n01060890/n01060890.github.io/code/html/hive.jpg

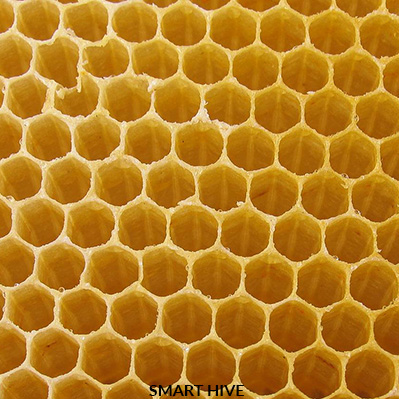
code/html/hive.jpg
