n01060890/n01060890.github.io/media/budget.jpg

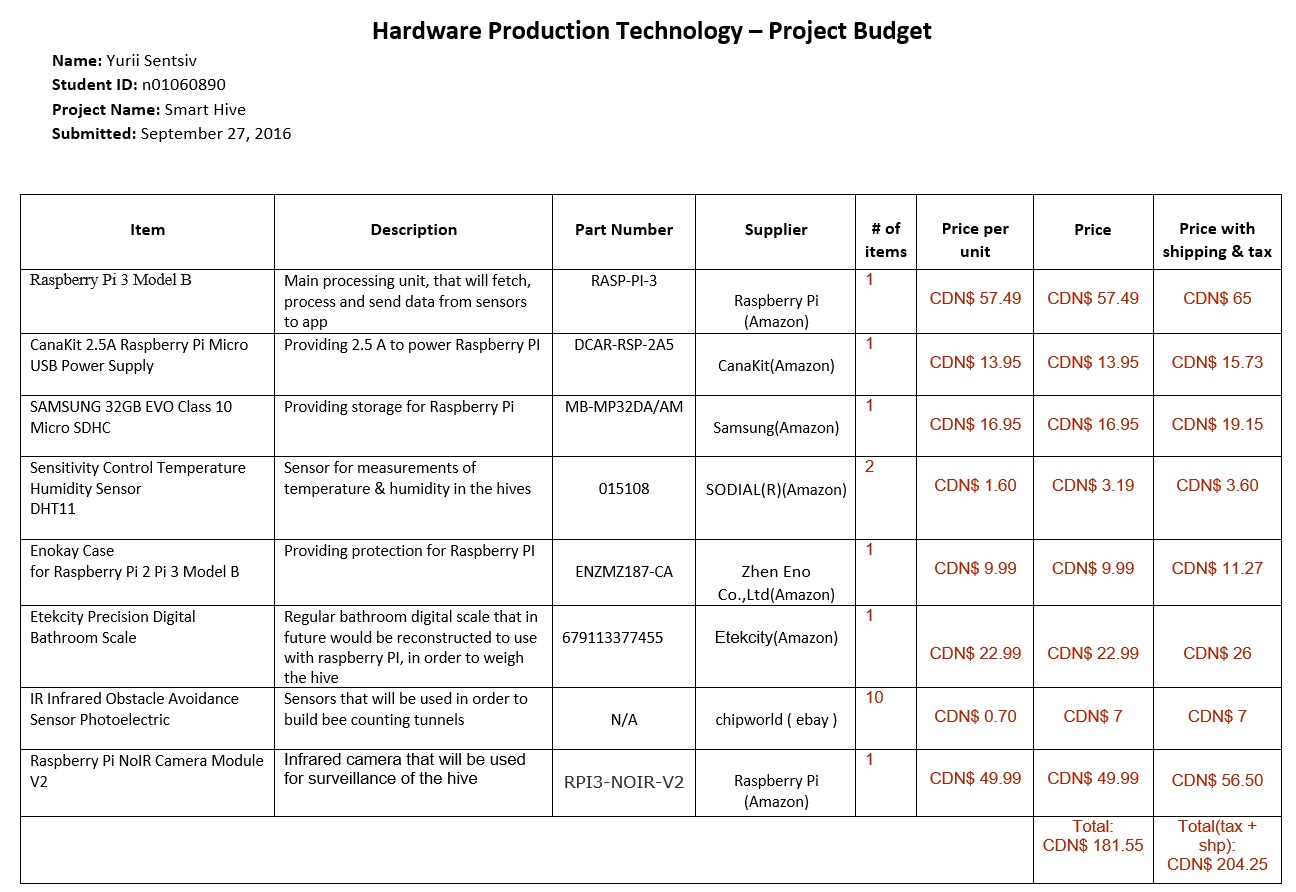
media/budget.jpg
