n01060890/n01060890.github.io/media/case.jpg

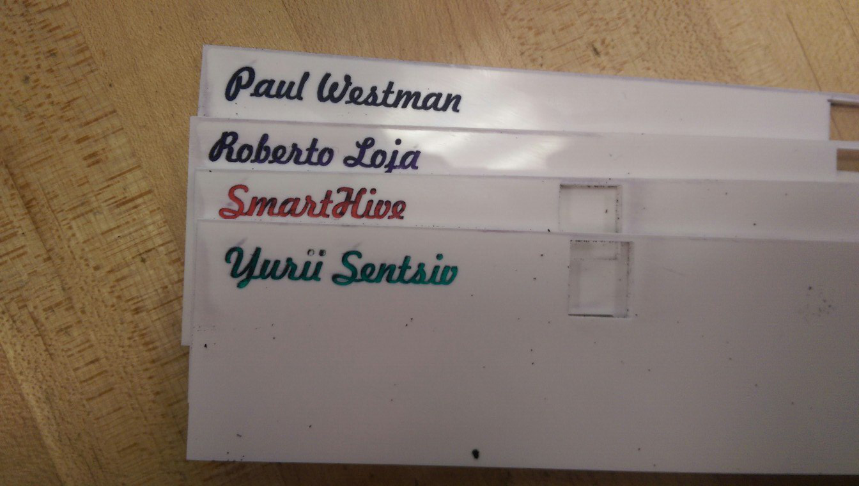
media/case.jpg
