n01060890/n01060890.github.io/media/cluster.png

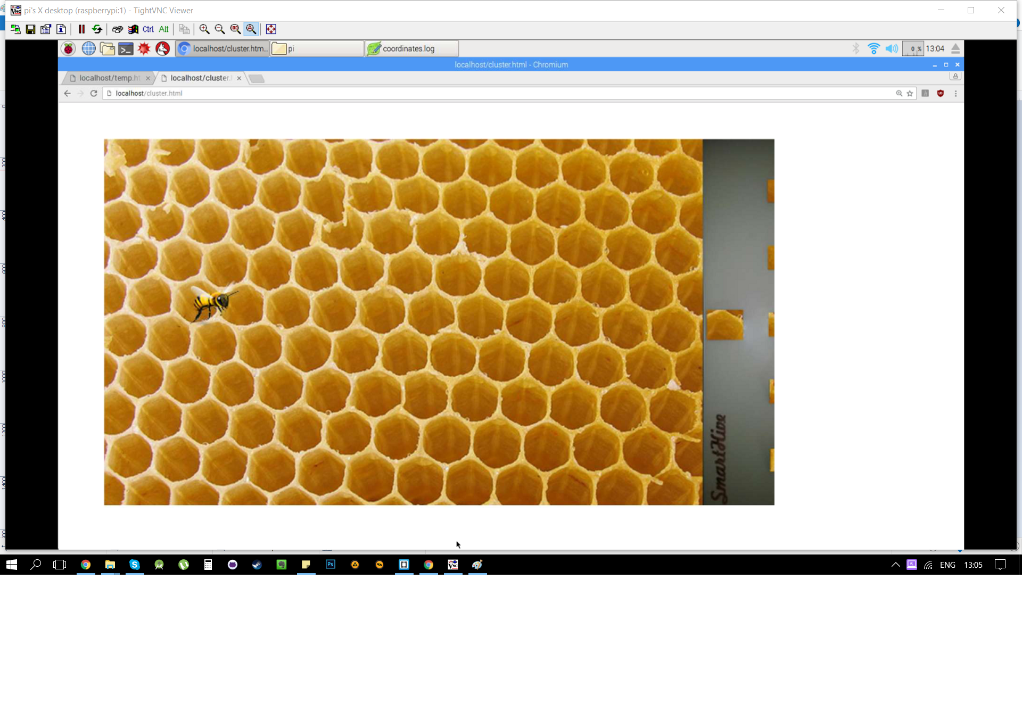
media/cluster.png
