n01060890/n01060890.github.io/media/crontab.png

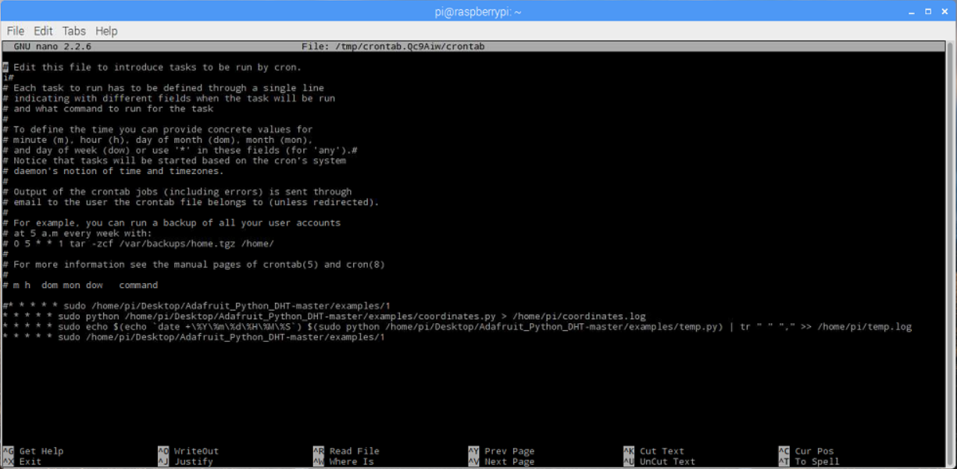
media/crontab.png
