n01060890/n01060890.github.io/media/DHT11.jpg

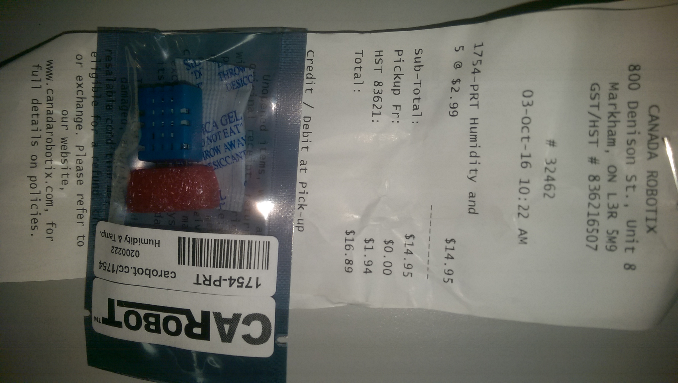
media/DHT11.jpg
