n01060890/n01060890.github.io/media/dht11_pcb.jpg

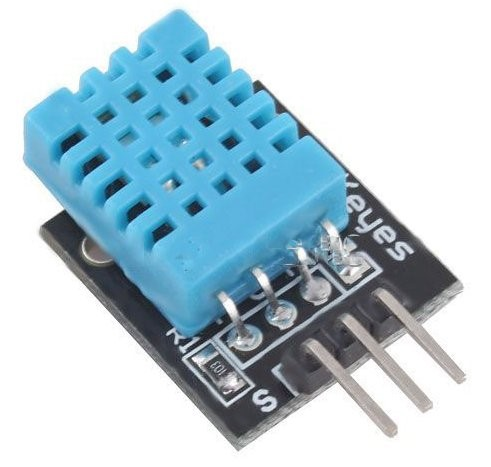
media/dht11_pcb.jpg
