n01060890/n01060890.github.io/media/dht11_pcb_mine.png

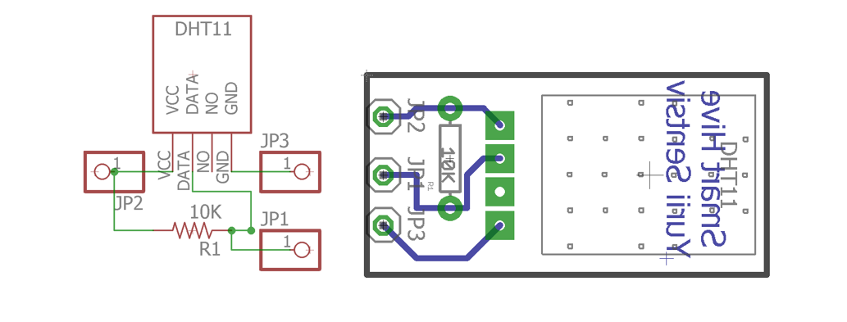
media/dht11_pcb_mine.png
