n01060890/n01060890.github.io/media/dht11_taped.jpg

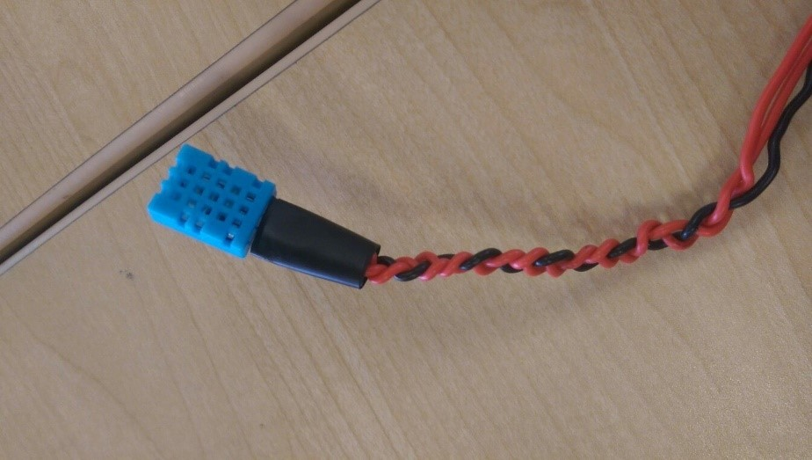
media/dht11_taped.jpg
