n01060890/n01060890.github.io/media/laser_cut.png

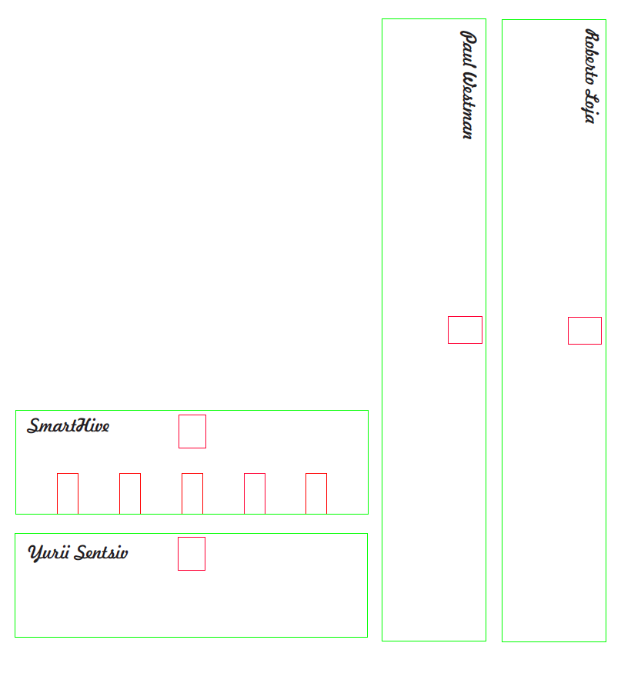
media/laser_cut.png
