n01060890/n01060890.github.io/media/LEDBLINK.jpg

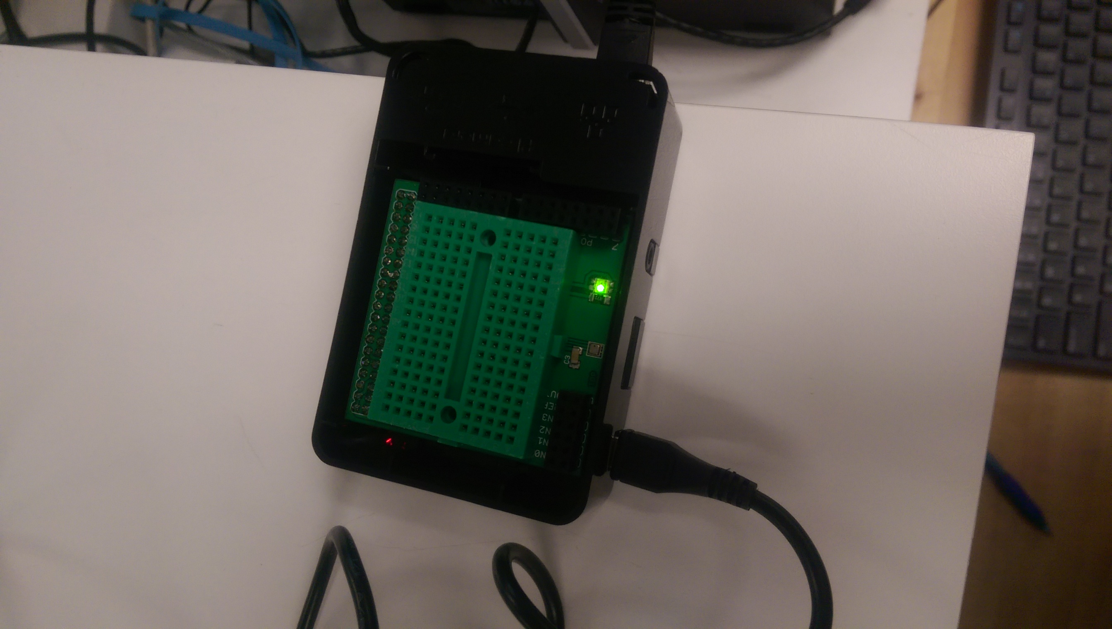
media/LEDBLINK.jpg
