n01060890/n01060890.github.io/media/MultiSensor1.jpg

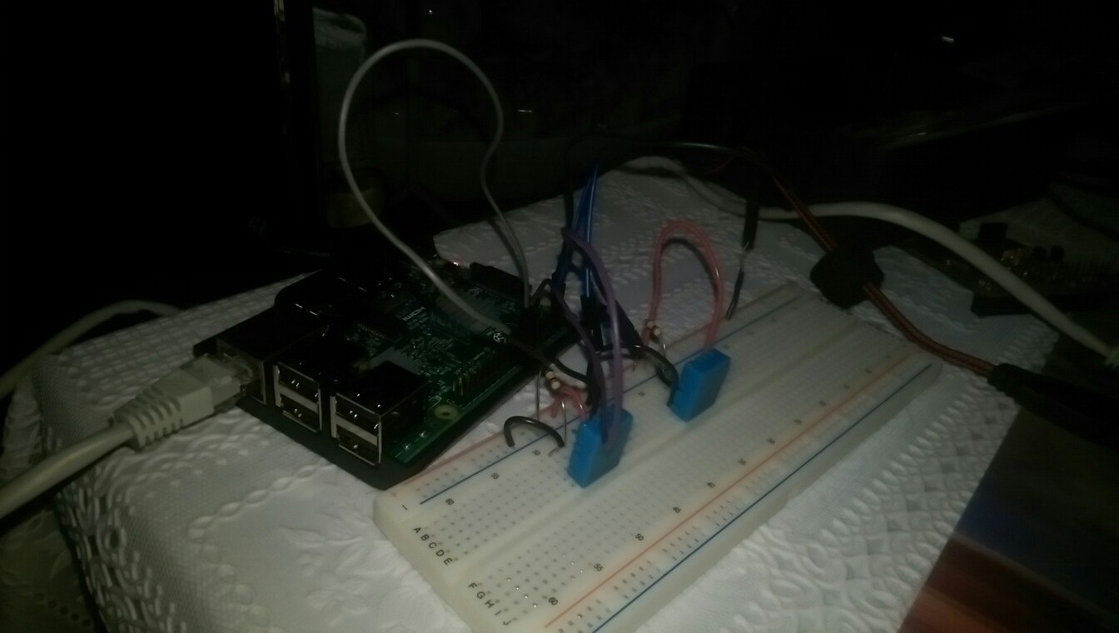
media/MultiSensor1.jpg
