n01060890/n01060890.github.io/media/MultiSensor2.jpg

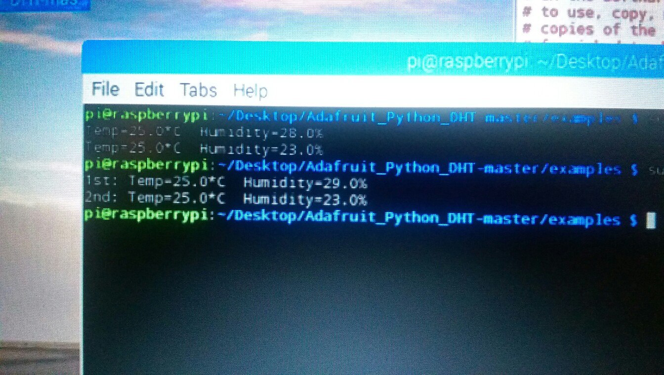
media/MultiSensor2.jpg
