n01060890/n01060890.github.io/media/myPCB.jpg

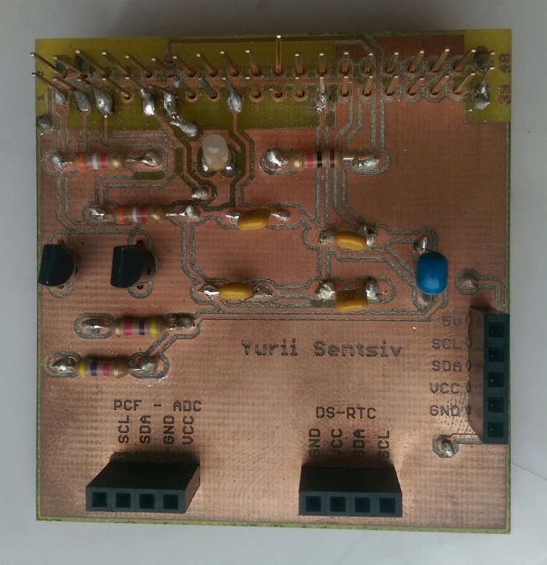
media/myPCB.jpg
