n01060890/n01060890.github.io/media/OHouse1.jpg

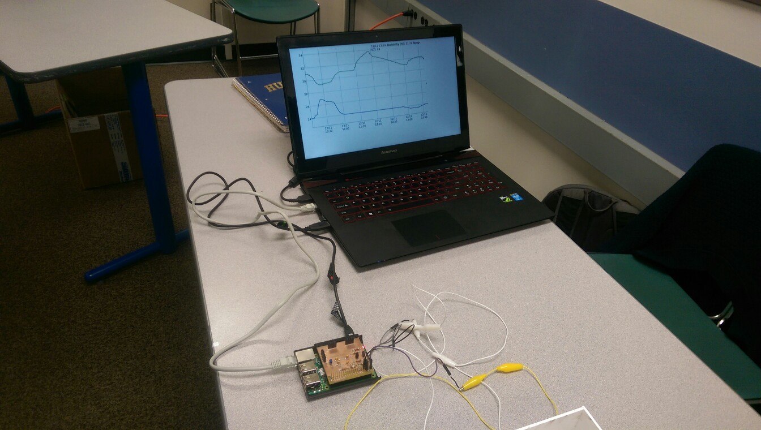
media/OHouse1.jpg
