n01060890/n01060890.github.io/media/OHouse2.jpg

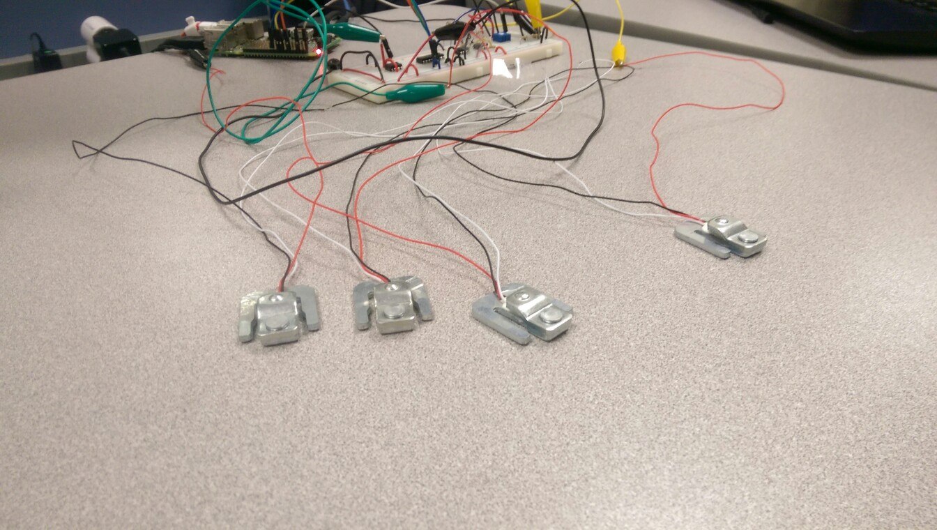
media/OHouse2.jpg
