n01060890/n01060890.github.io/media/OHouse3.jpg

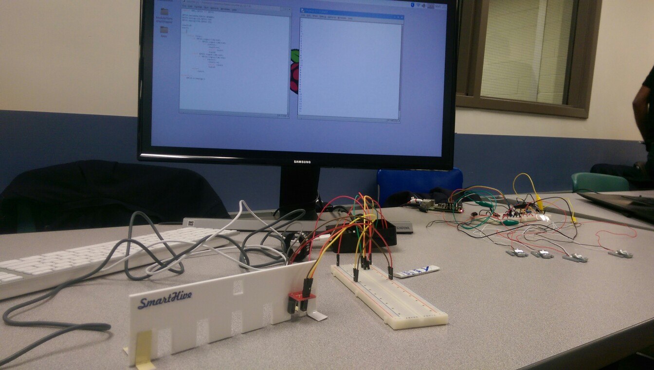
media/OHouse3.jpg
