n01060890/n01060890.github.io/media/output_screen.png

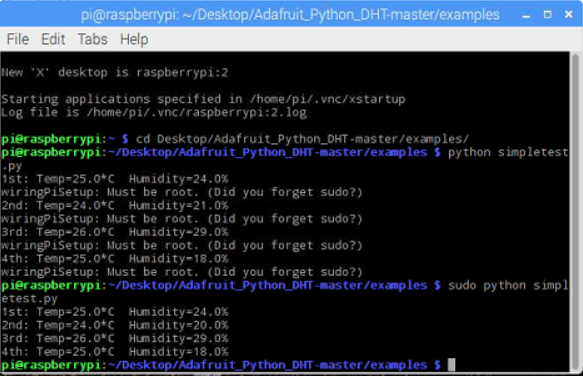
media/output_screen.png
