n01060890/n01060890.github.io/media/PCB_board.png

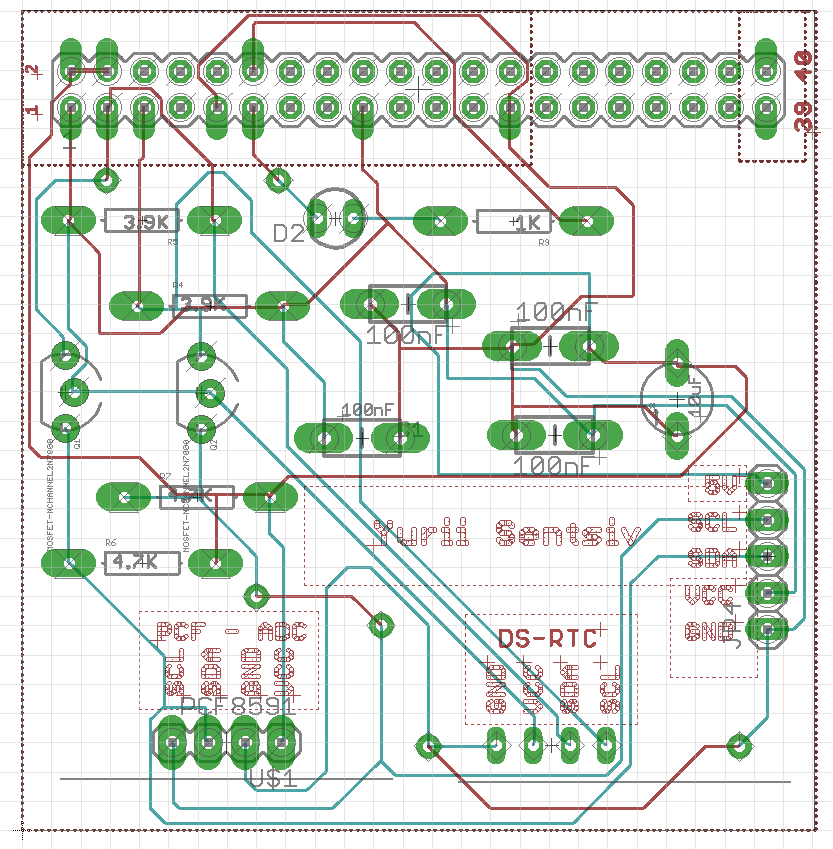
media/PCB_board.png
