n01060890/n01060890.github.io/media/PCB_scheme.png

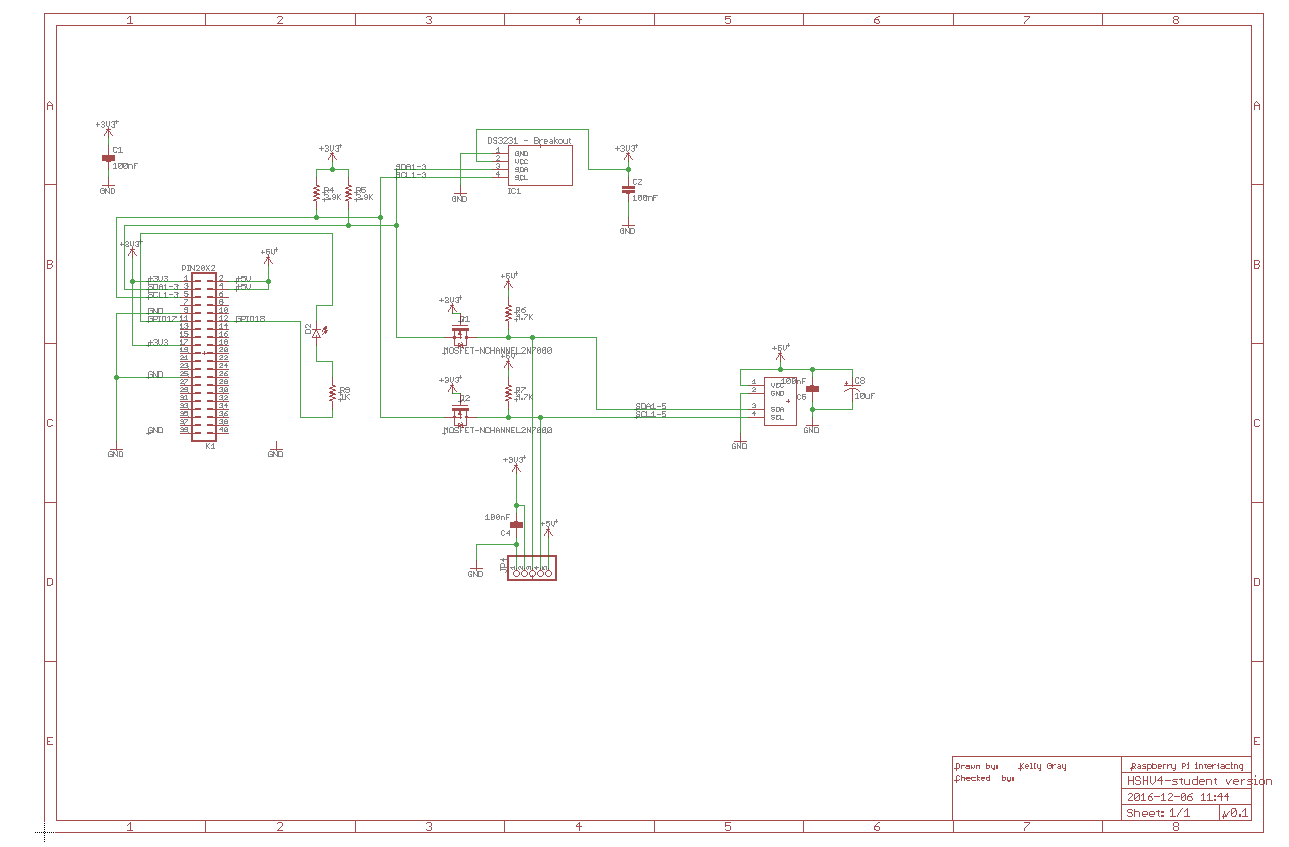
media/PCB_scheme.png
