n01060890/n01060890.github.io/media/project-scedule.jpg

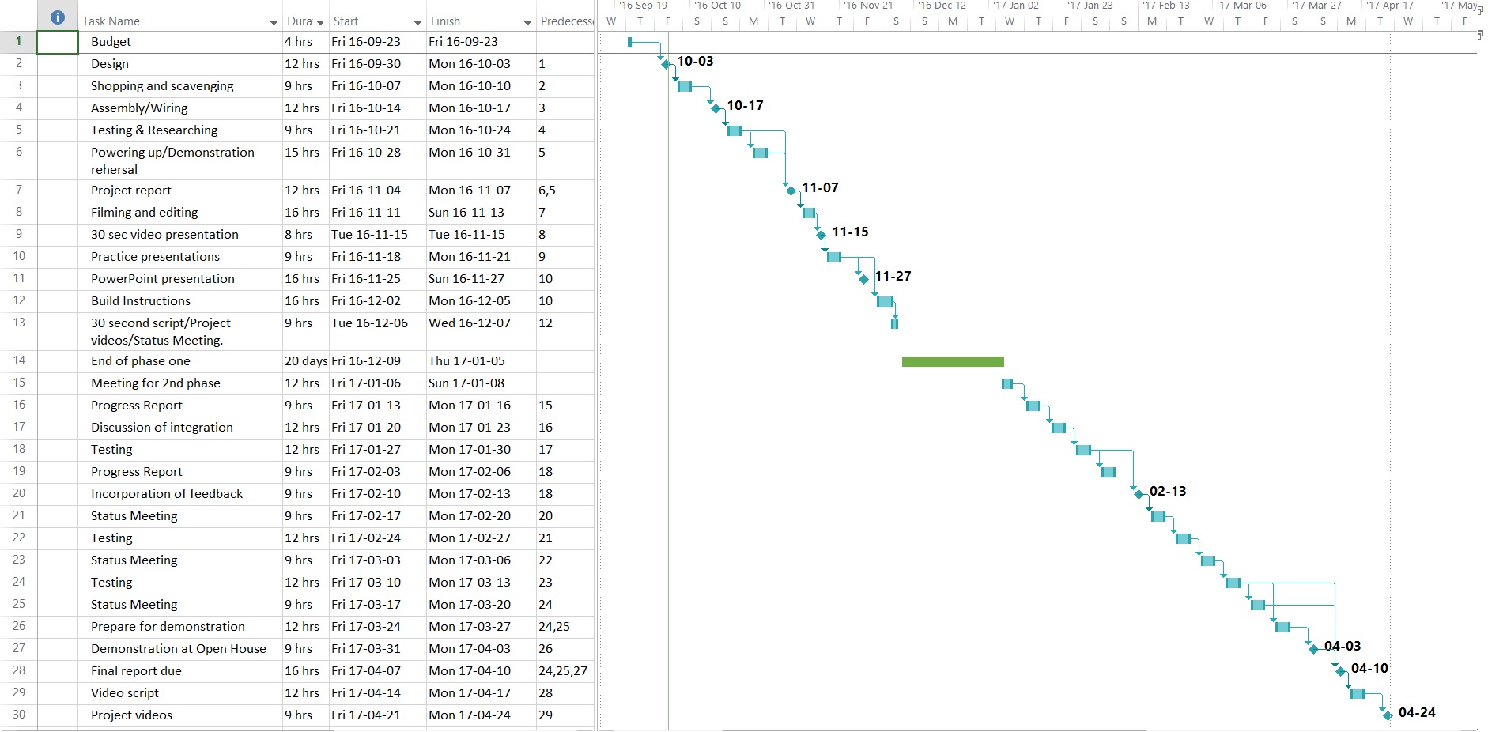
media/project-scedule.jpg
