n01060890/n01060890.github.io/media/scheme.png

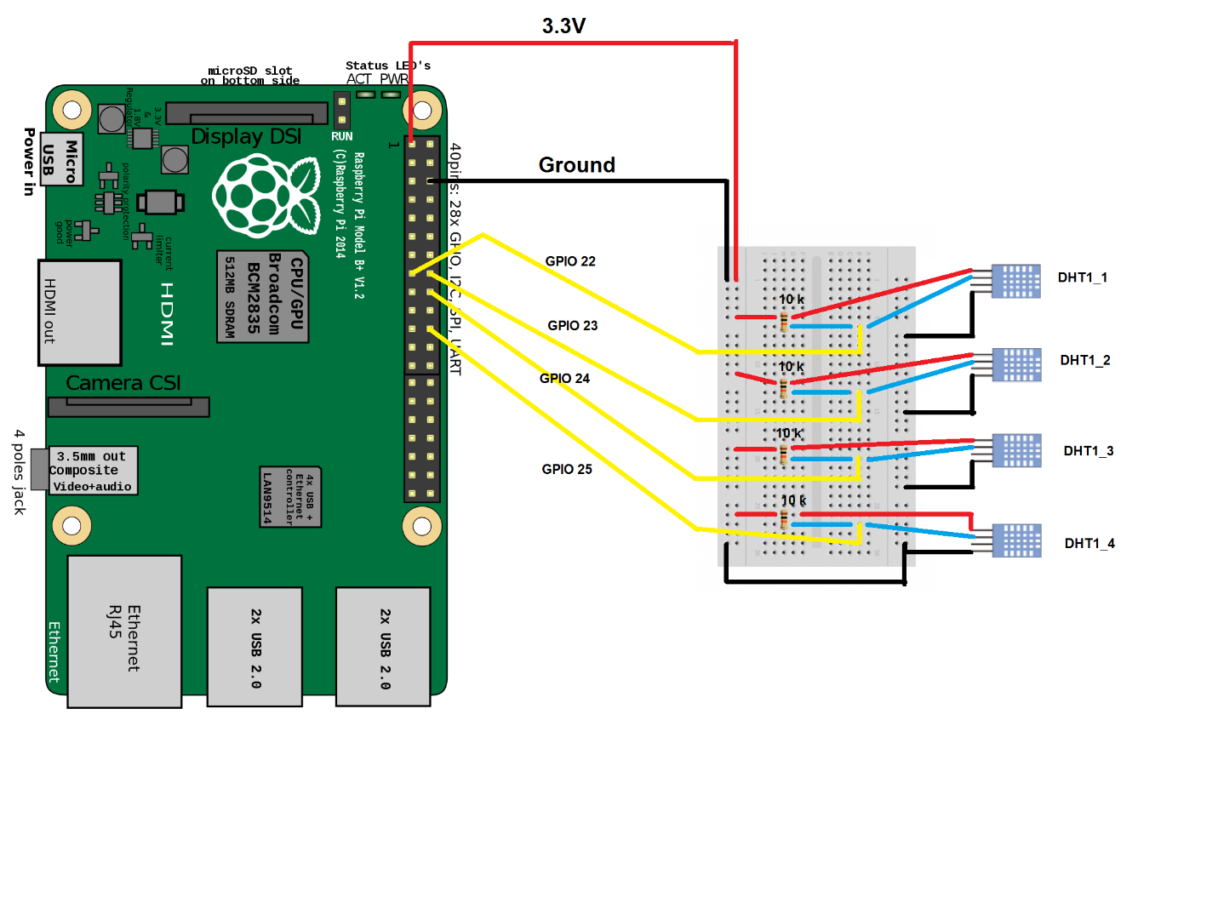
media/scheme.png
