n01060890/n01060890.github.io/media/sys_diagram.jpg

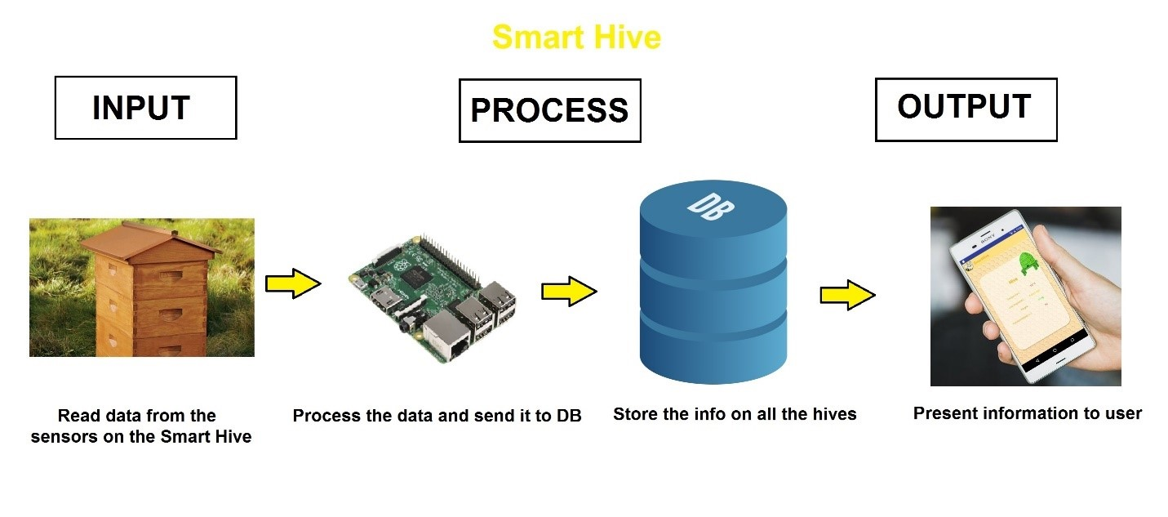
media/sys_diagram.jpg
